Theo824/Solar-Charger/PCB_Pics/solarChargerPCBpic.jpg

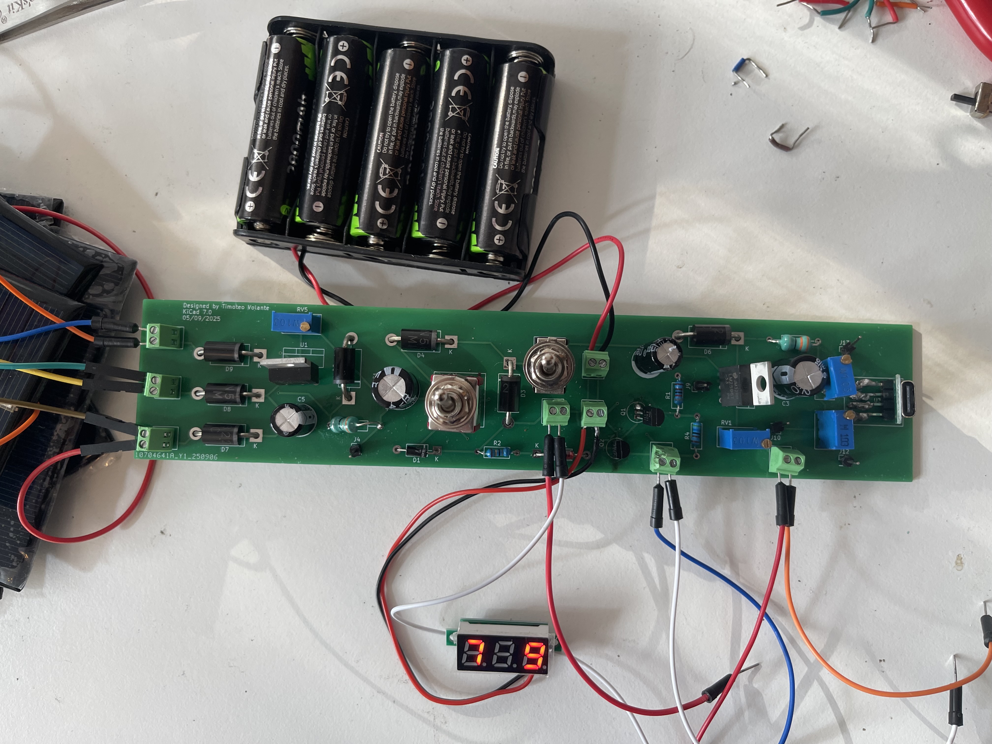
PCB_Pics/solarChargerPCBpic.jpg
