Theo824/Solar-Charger/Testing_Pics/breadboardTest.jpg

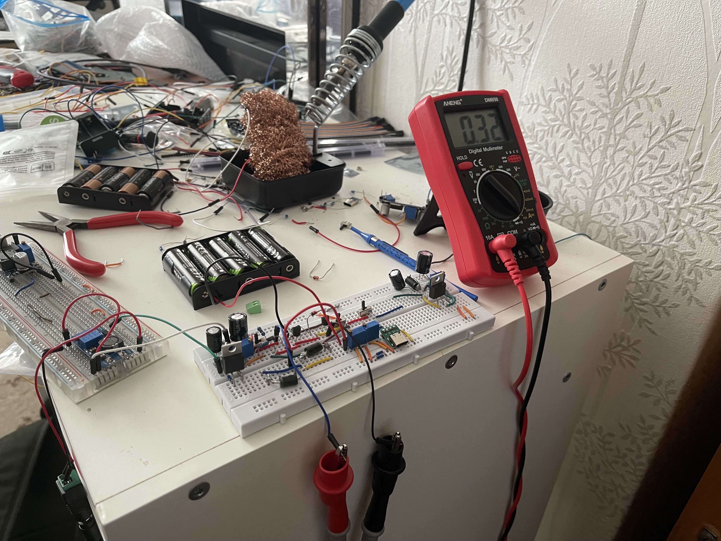
Testing_Pics/breadboardTest.jpg
