Theo824/Solar-Charger/Testing_Pics/iPhone5WCharg.JPG

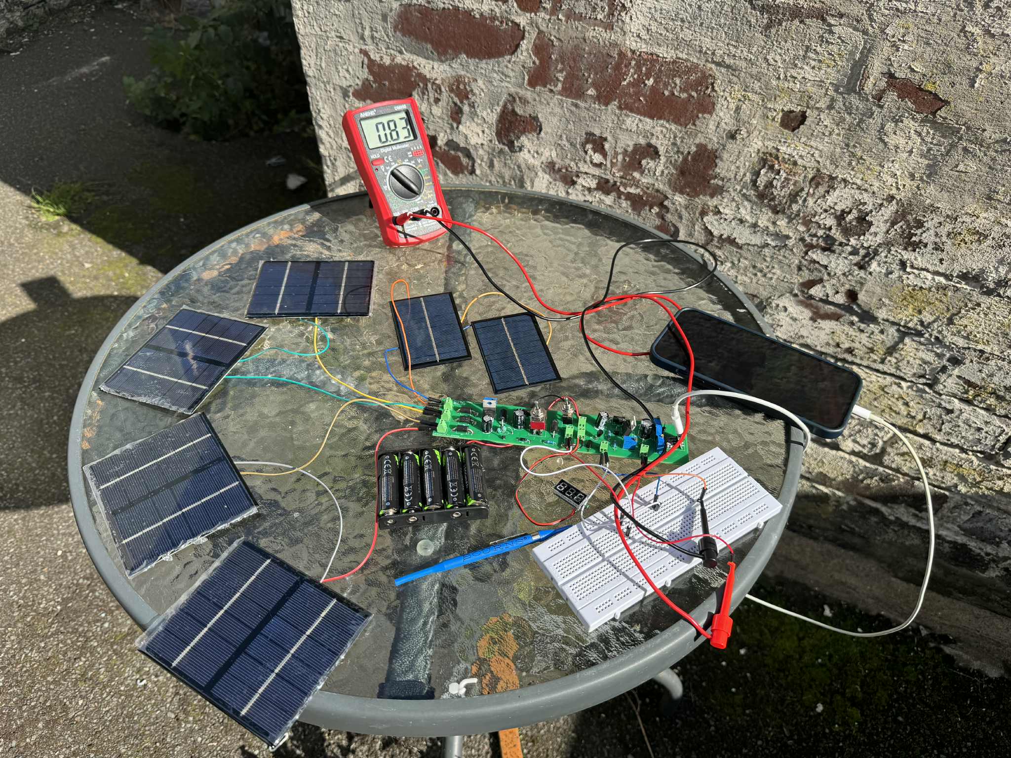
Testing_Pics/iPhone5WCharg.JPG
