Theo824/Solar-Charger/Testing_Pics/iPhoneChargeGraph1.png

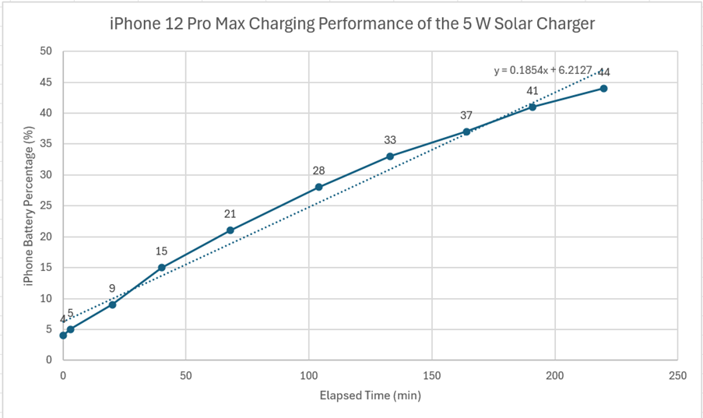
Testing_Pics/iPhoneChargeGraph1.png
