Theo824/Solar-Charger/Testing_Pics/NiMH_PCB_CutOff.png

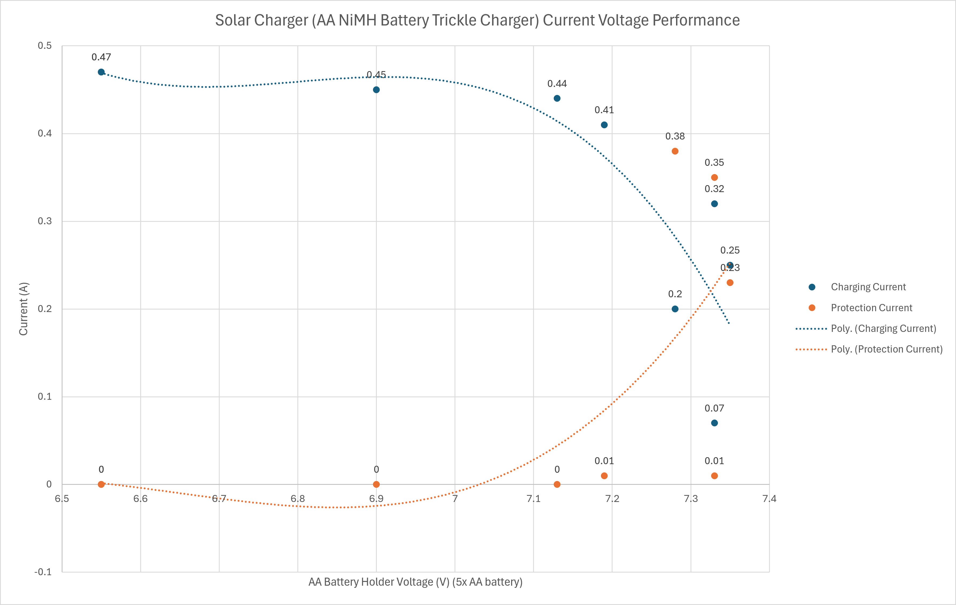
Testing_Pics/NiMH_PCB_CutOff.png
