Theo824/Solar-Charger/Testing_Pics/NiMH_PCB_CutOff_Data_Table.png

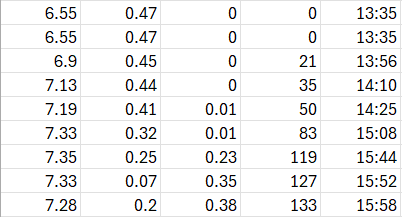
Testing_Pics/NiMH_PCB_CutOff_Data_Table.png
