Theo824/Solar-Charger/Testing_Pics/breadboardTest_iPhone.jpg

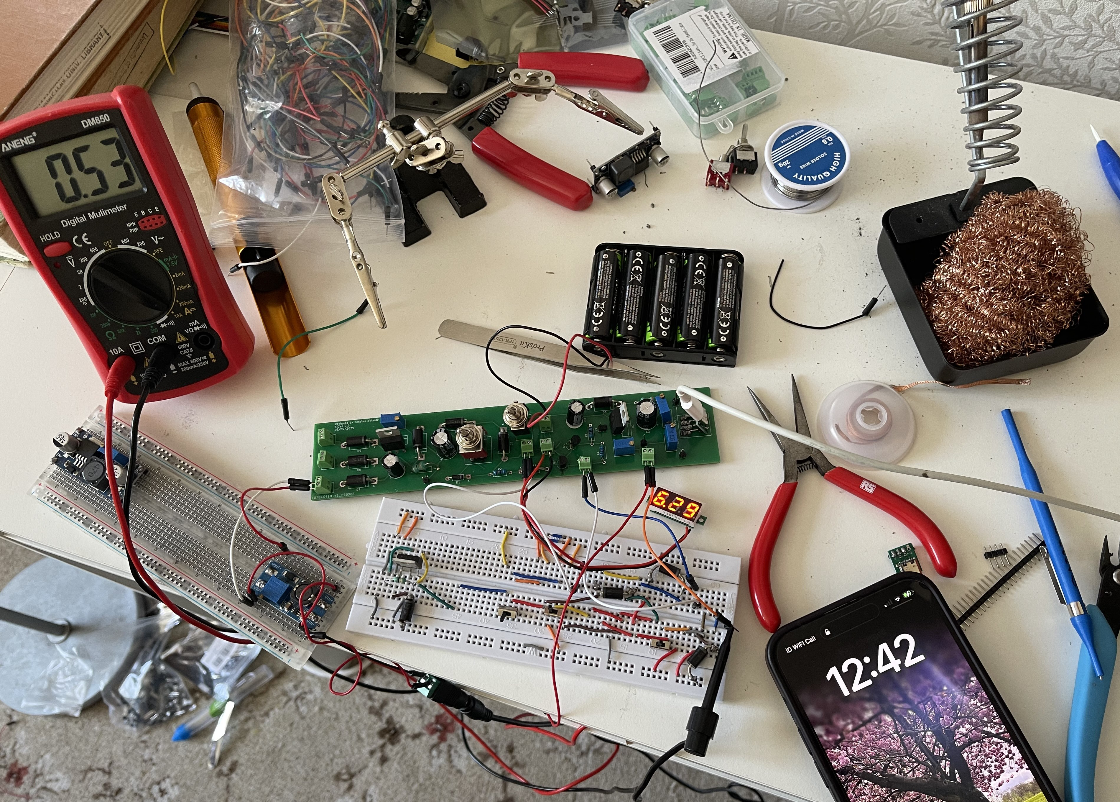
Testing_Pics/breadboardTest_iPhone.jpg
